rimtty/RoadWeave/docs/megachips-rfq-draft.md

# MegaChips MRF61_A 問い合わせ文面（下書き、Issue #10）

送付前に会社名・用途・数量の想定を埋める。技術質問は「はい/いいえ」で答えられる形にしてある。

---

件名: MRF61_A（Wi-Fi HaLow モジュール）の MCU ホスト利用と少量調達について

MegaChips 様

車両間の音声・位置情報共有端末（免許不要の 920 MHz 帯 802.11ah、PTT 型グループ通話）を開発しております〇〇の〇〇と申します。
貴社 MRF61_A の採用を検討しており、以下についてご教示ください。

1. ホスト接続
   - ESP32-S3 などの MCU から SPI で接続し、Morse Micro の MM-IoT-SDK（ESP-IDF 向け component）で駆動することは可能でしょうか。
   - MRF61_A 用の BCF（Board Configuration File）は貴社から提供されますか。Morse Micro の SDK に同梱されるものと同一でしょうか。
   - Linux（SDIO）以外の MCU ホスト向けの技術サポート窓口はありますか。
2. 国内制度への適合
   - JP モードで、キャリアセンス 5 ms 以上 / 送信時間 4 s 以内 / 休止 50 ms 以上（920.5〜923.5 MHz）の条件は
     モジュールのファームウェアまたはドライバ側で保証されますか。アプリケーション側で必要な制御があれば教えてください。
   - 923.5 MHz 以下に収まる 1 MHz / 2 MHz チャネルの番号と op-class をご教示ください。
   - 工事設計認証に登録されているアンテナの型式・利得の一覧、および外部アンテナ（車載マグネット型など）を追加登録する手続きをご教示ください。
3. 調達
   - 評価キット（MCU 向け）の型番と入手方法。
   - 100 / 1,000 / 10,000 台での単価目安、MOQ、リードタイム。
   - 国内代理店があれば窓口を教えてください。
4. 資料
   - データシート、リファレンス回路、レイアウトガイド（RF keep-out、電源要件）の入手方法。

用途: 車両間グループ音声（Opus 12 kbps、UDP）と 1 Hz の位置ビーコン。想定台数は初期 100 台、量産時 1,000 台規模です。

よろしくお願いいたします。

〇〇（会社名 / 氏名 / 連絡先）
---
