rimtty/RoadWeave/firmware/boards/heltec_hc01p/hc01p_pin_map.jpg

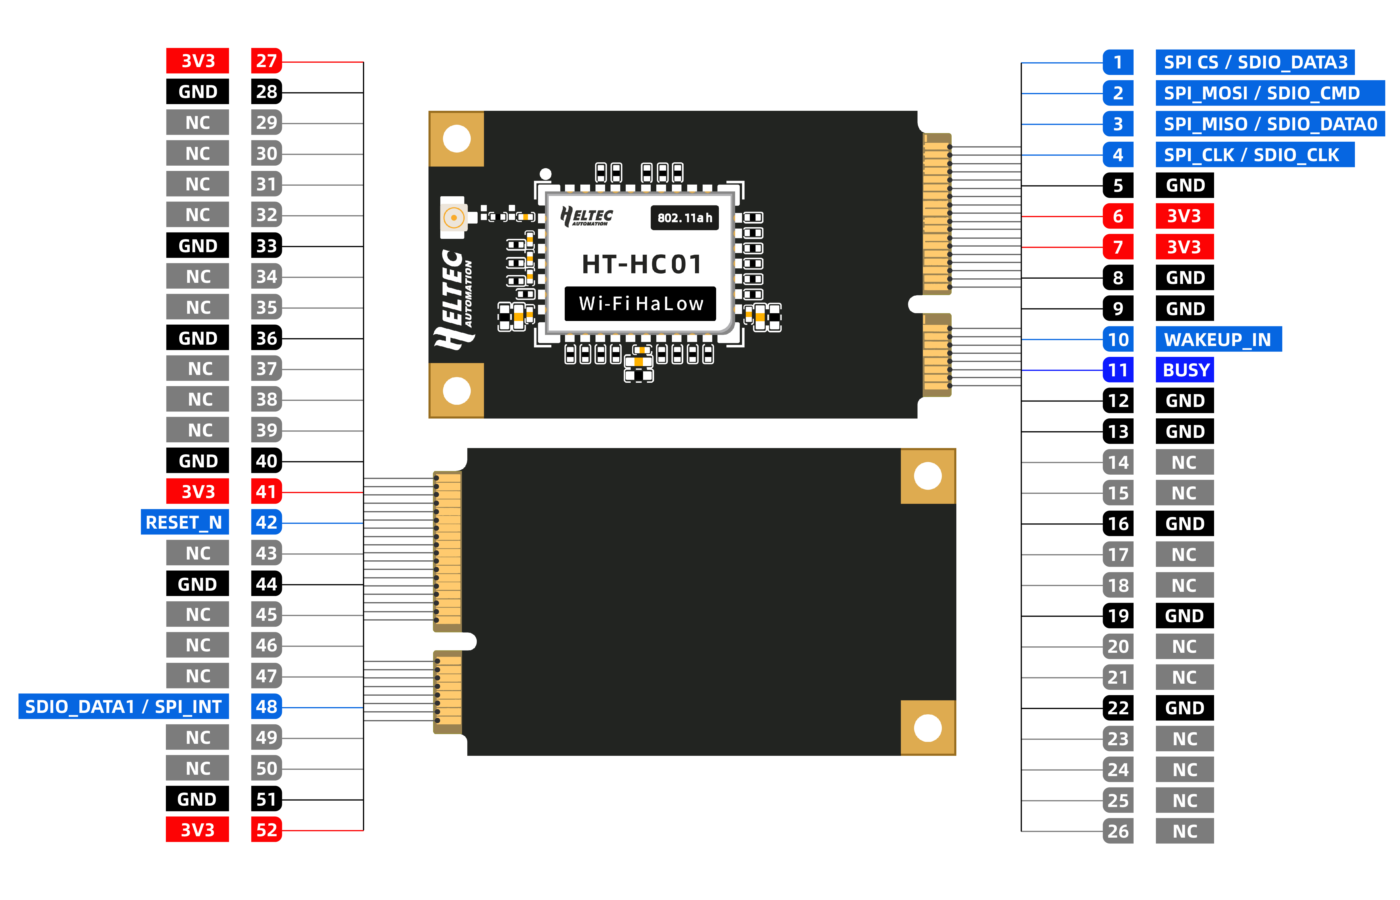
firmware/boards/heltec_hc01p/hc01p_pin_map.jpg
