rimtty/RoadWeave/docs/bringup/logs/2026-09-05-p0a-gate1-node1.md

# P0-A Gate 1 test log: XIAO単体smoke（1台目）

## Test metadata

| Field | Value |
|---|---|
| Date/time | 2026-09-05 23:06 JST |
| Operator | rimtty（Claude Code経由でflash/monitor） |
| Git commit | f41c152 |
| ESP-IDF | v5.4.4（`idf.py --version`でcheck-toolchain PASS） |
| Morse component | 2.11.2-esp32-2（本firmwareでは未使用） |
| Host computer / OS | Apple Silicon Mac / macOS 27 |
| RF setup | disabled（WM6180未装着、HaLow未初期化） |
| USB port | `/dev/cu.usbmodem31201`（USB Serial/JTAG、VID 303A / PID 1001） |

## Node inventory

| Node | XIAO visual ID | WM6180 visual ID | USB port | Stack photo | Result |
|---|---|---|---|---|---|
| RW-N0?（要割り当て） | header実装済み個体 1台目 | 未装着 | usbmodem31201 | n/a | Gate 1 PASS |

Node IDはXIAO本体へラベルを貼ってから確定する。残り2台は未実施。

## Gate 1: XIAO-only smoke

| Node | Flash MiB | PSRAM initialized | PSRAM MiB | `P0A_XIAO_SMOKE` | Replug boot | Result |
|---|---:|---|---:|---|---|---|
| 1台目 | 8 | yes | 8 | PASS | RTS reset後の再bootで同一log | PASS |

補足: esptool単体でも同じ個体を確認済み（ESP32-S3 rev v0.2、flash GD 8MB quad、Embedded PSRAM 8MB AP_3v3）。

## Raw log（app部分、boot ROM/bootloader行は省略）

```text
I (516) roadweave: RoadWeave P0-A XIAO board smoke test
I (516) roadweave: ESP-IDF: v5.4.4
I (516) roadweave: Chip: model=9 cores=2 revision=2
I (516) roadweave: Internal heap: free=8744720 minimum=8744720 bytes
I (516) roadweave: Flash: 8388608 bytes (8 MiB)
I (516) roadweave: PSRAM: initialized=yes physical=8388608 bytes heap_total=8388608 bytes free=8386188 bytes
I (516) roadweave: P0A_XIAO_SMOKE=PASS
W (516) roadweave: HALOW_TX=DISABLED: this firmware does not initialize WM6180/MM6108
```

bootloader logの要点: `octal_psram: density 64 Mbit`、`esp_psram: Found 8MB PSRAM device`、`SPI SRAM memory test OK`、`spi_flash: detected chip: gd`、`flash io: qio`。

## Decision

- [x] Proceed to next gate（この個体はGate 2へ進める。残り2台のGate 1が必要）
- [ ] Repeat with corrected setup
- [ ] Stop and open a blocking issue

Reason: 期待値（8 MiB flash、8 MiB Octal PSRAM、USB Serial/JTAG console）をすべて満たした。
