rimtty/RoadWeave/docs/bringup/halow-wide-performance-report-2026-09-20.md

# Wio-WM6180 4/8 MHz帯域と7 Mbps到達試験（2026-09-20）

対象はXIAO ESP32-S3からSPI接続したWio-WM6180（MM6108）を2台使うUDP一方向通信。ESP32内蔵2.4/5 GHz Wi-Fiは使っていない。アンテナ装着済みのCOM4をAP、COM5をSTAとし、COM6は試験対象外とした。使用場所は依頼者がUS設定の条件を確認済み。試験はすべて有限時間、TX出力はSDK設定値1 dBmで、実放射電力の測定ではない。

## 判定方法

1200 B UDP payload（16 B試験header、1184 B検証body）を送受信し、受信側でsequenceとbodyを検証した。主指標はDATA窓のunique受信bytesから求めたUDP payload goodputで、END後のtailは加えない。送信の目標追随95%以上、active/final受信率99%以上などの条件を60秒×3回すべて満たした最高の**指定rate**と、高負荷stageの**最大観測受信goodput**を別々に扱う。PHYの理論値とは比較しない。探索の30秒stageと無制限送信stageは、60秒×3回の持続合格を意味しない。

チャネルはUS設定で2 MHz=905 MHz/ch6/class2、4 MHz=914 MHz/ch24/class3、8 MHz=916 MHz/ch28/class4。各測定でAPとSTAの接続後チャネル・帯域幅が指定と一致することを確認した。中心周波数も変わるため、測定差を帯域幅だけの効果とは断定しない。モジュールの[FGH100M-H公式仕様](https://www.quectel.com/product/wi-fi-halow-fgh100m-h/)は902–928 MHzおよび1/2/4/8 MHz対応を示すが、本測定はUS向けreference構成の確認であり、日本向け製品の適合性の根拠ではない。

## 結果

| 幅 | 方向 | 60秒×3で合格した最高指定rate | 3回の受信UDP goodput | 最大観測受信UDP / body goodput |
|---|---|---:|---:|---:|
| 2 MHz（診断付き対照） | STA→AP | 2.5 Mbps | 2.413–2.428 Mbps | 3.181 / 3.138 Mbps |
| 4 MHz | STA→AP | 2.0 Mbps | 1.957–1.962 Mbps | 3.684 / 3.635 Mbps |
| 4 MHz | AP→STA | 2.0 Mbps | 1.956–1.957 Mbps | 3.671 / 3.622 Mbps |
| 8 MHz | STA→AP | 2.0 Mbps | 1.953–1.954 Mbps | 3.665 / 3.616 Mbps |
| 8 MHz | AP→STA | 2.0 Mbps | 1.944–1.945 Mbps | 3.657 / 3.609 Mbps |

最大観測は有効な本測定stageからwarmupを除いて選んだ。2 MHzは新しい診断付きFWのSTA→AP対照で、前回の4条件測定値とは別caseである。4/8 MHzの最大観測では実送信も約3.67–3.70 Mbpsだった。4/8 MHz間の約0.03 Mbps差を有意な帯域効果とは見なさない。

7 Mbpsは今回の構成では観測されなかった。8 MHzの指定負荷を32 Mbpsまで上げても、STA→APの最大観測受信UDPは3.665 Mbps、AP→STAは3.657 Mbpsだった。これはMM6108や8 MHz無線の絶対上限ではない。高負荷時の実送信が約3.6–3.7 Mbpsで頭打ちになり、受信側の良否以前に送信側が目標rateへ追随できていない。`send()`、body生成・検証、SPI/IRQ、RF rate controlの寄与は未分離である。

4/8 MHzの2.5 Mbps指定でも実送信/指定は94.0–94.45%で、合格条件の95%を下回った。受信率だけを見て2.5 Mbpsを合格へ繰り上げていない。[FGH100M-H公式仕様](https://www.quectel.com/product/wi-fi-halow-fgh100m-h/)の最大32.5 MbpsはPHY値であり、このESP32-S3・SPI・UDP検証経路の保証goodputではない。

8 MHz AP→STAでは128/256 kbpsの短い探索点で受信率が98.75%/98.12%となり、512 kbps以上の一部は合格した。初回の低負荷不合格を速度上限とみなさず、予定した全探索点と反復を記録した。目標rateへの追随不足と無線損失を混同しない。

## 実機で見つかった4 MHz起動不具合

最初の4 MHz smokeはAPのsupplicant設定読込み時に失敗し、stage 0で終了した。試験ファームウェアが運用チャネルを1件だけSDKへ渡し、AP設定生成が必要とする帯域内の2 MHzプライマリチャネルを見つけられなかった。修正では選択した運用チャネルに加え、その帯域に収まる1/2 MHzサブチャネルをSDKのリストに残す。運用チャネルを示す先頭要素は固定し、接続後の実チャネル確認もその要素と照合する。修正後の4 MHz、8 MHz smokeは両端の実動作幅と正常停止を確認して通過した。

共有リポジトリのチェックアウトが途中で別作業によりmainへ切り替わり、4 MHz逆方向の最初の再書込みには修正前sourceが入った。この試験はAP起動前のstage 0失敗として保存した。保存済み修正版バイナリをハッシュ確認してCOM4/5へ直接書き、両端のflash照合を通した後に逆方向を再実行した。失敗試験を成功例へ混入しない。

## 来歴と終了状態

公開した[集計と非秘密カウンタ](logs/2026-09-20-wide/metrics.json)に、各stageの実送信・受信・損失・判定、バイナリSHA256、private原本のSHA256を保存する。PSK、SSID、raw SDKログとprivate設定は公開しない。

8 MHzの2件のhost `report.json`では、試験開始時のHEADをファームウェアsource commitとして記録してしまい、共有チェックアウト後のmain `043471f`が表示された。8 MHz AP/STAは切替前に`bcfd652`上でビルドされ、同じSHA256のバイナリで切替前のsmokeを通した。さらに両端の実機ログは修正版固有の`entries=13`を出している。公開集計では**原記録**と**検証したsource帰属**を併記し、黙って原本を書き換えない。今後のrunnerは実際にflashしたバイナリのsourceを明示して固定する。

COM4/5は保存済みの通常`aa58241` 1 MHz DHCPファームウェアへ戻し、MACとflashの一致を確認した。COM6は同sourceのSTA2 imageのflash一致を確認した。[最終状態](logs/2026-09-20-wide/final-state.json)に3個体のMAC、バイナリSHA256、有限通信試験と停止証拠を記録した。

復元後の3台・60秒通信ではウォームアップ後STA1/STA2がともに188/188応答だったが、runner既定の120秒・200送信以上を満たさないため総合FAILのままとした。160秒の1回目は通信断が生じ、ウォームアップ後447/475と512/526で99%受信率を下回りFAIL。変更なしで実施した2回目は548/548と582/583、同時観測146.89秒でPASSした。**1回の再試験合格で先の通信断を消さない。** 今回の通常構成は通信可能で最終停止も完了したが、3台同時運用の品質はこの2回で変動しており、安定性の原因は未特定である。

最終試験ではCOM4/5/6すべてにSTOP、radio shutdown、`RW_LINK_RADIO_RESULT=PASS`、DONEを確認した。現在の3台は無線停止状態。通常FWを再起動・再給電すると最大600秒の有限1 MHz試験が始まる設定であり、電源を物理的に遮断した状態ではない。
