rimtty/RoadWeave/firmware/experiments/ui_lvgl/pc/baselines/busy.png

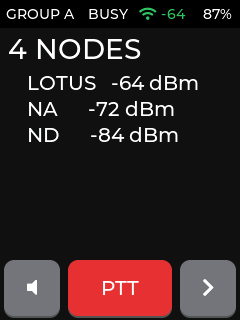
firmware/experiments/ui_lvgl/pc/baselines/busy.png
