rimtty/RoadWeave/firmware/experiments/ui_lvgl/pc/baselines/dot14.png

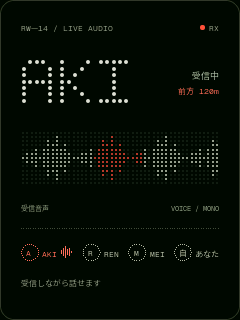
firmware/experiments/ui_lvgl/pc/baselines/dot14.png
