rimtty/RoadWeave/firmware/experiments/ui_lvgl/pc/baselines/dot15.png

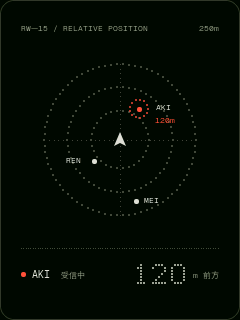
firmware/experiments/ui_lvgl/pc/baselines/dot15.png
