rimtty/RoadWeave/firmware/experiments/ui_lvgl/pc/baselines/dot16.png

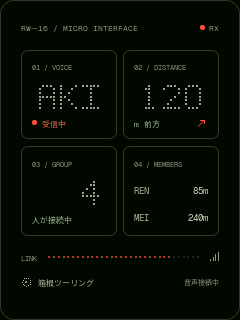
firmware/experiments/ui_lvgl/pc/baselines/dot16.png
