rimtty/RoadWeave/firmware/experiments/ui_lvgl/pc/baselines/dot_busy.png

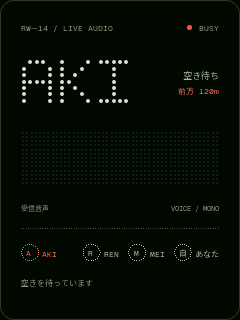
firmware/experiments/ui_lvgl/pc/baselines/dot_busy.png
