rimtty/RoadWeave/firmware/experiments/ui_lvgl/pc/baselines/dot_tx.png

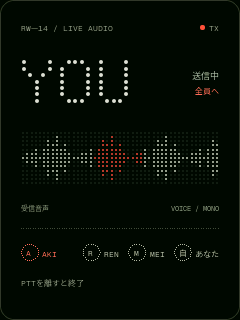
firmware/experiments/ui_lvgl/pc/baselines/dot_tx.png
