rimtty/RoadWeave/firmware/experiments/ui_lvgl/pc/baselines/empty.png

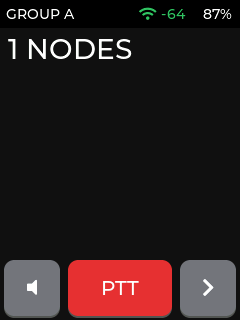
firmware/experiments/ui_lvgl/pc/baselines/empty.png
