rimtty/RoadWeave/firmware/experiments/ui_lvgl/pc/baselines/max_group.png

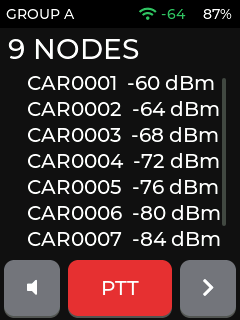
firmware/experiments/ui_lvgl/pc/baselines/max_group.png
