rimtty/RoadWeave/firmware/experiments/ui_lvgl/pc/baselines/radar_east.png

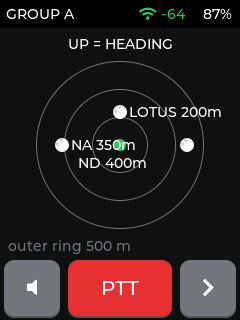
firmware/experiments/ui_lvgl/pc/baselines/radar_east.png
