rimtty/RoadWeave/firmware/experiments/ui_lvgl/pc/baselines/rx.png

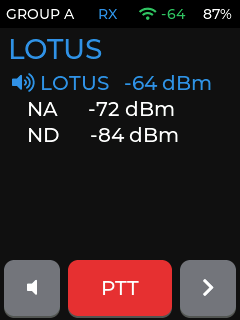
firmware/experiments/ui_lvgl/pc/baselines/rx.png
