rimtty/RoadWeave/firmware/experiments/ui_lvgl/pc/baselines/tx.png

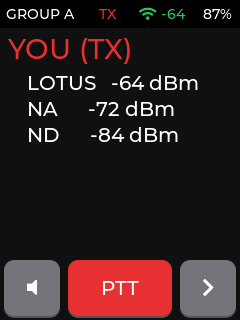
firmware/experiments/ui_lvgl/pc/baselines/tx.png
