rimtty/RoadWeave/firmware/experiments/ui_lvgl/pc/reference/web-dot13.png

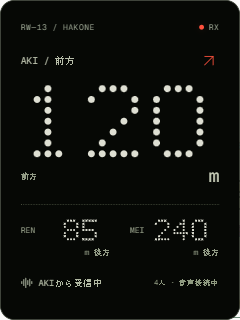
firmware/experiments/ui_lvgl/pc/reference/web-dot13.png
