rimtty/RoadWeave/firmware/experiments/ui_lvgl/pc/reference/web-dot14.png

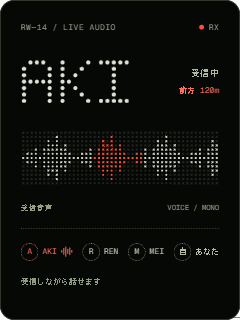
firmware/experiments/ui_lvgl/pc/reference/web-dot14.png
