rimtty/RoadWeave/firmware/experiments/ui_lvgl/pc/reference/web-dot16.png

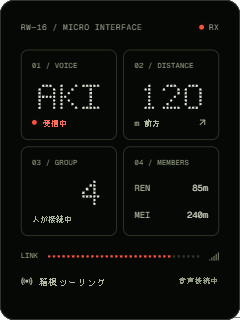
firmware/experiments/ui_lvgl/pc/reference/web-dot16.png
